YuhKuro/Numlocked/pictures/Front.png

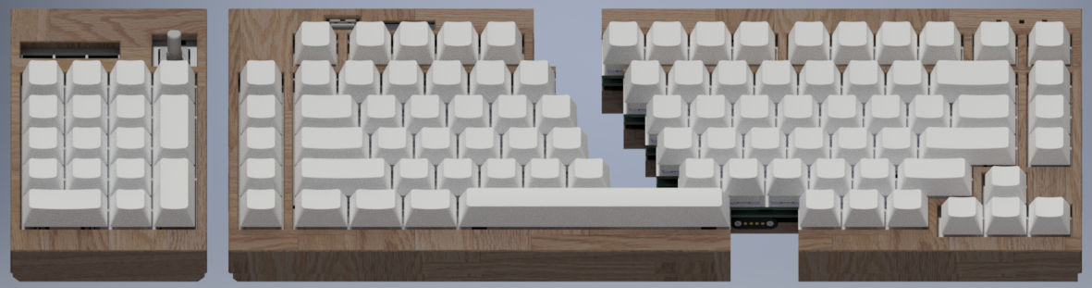
pictures/Front.png
