YuhKuro/Numlocked/pictures/GUIExample.png

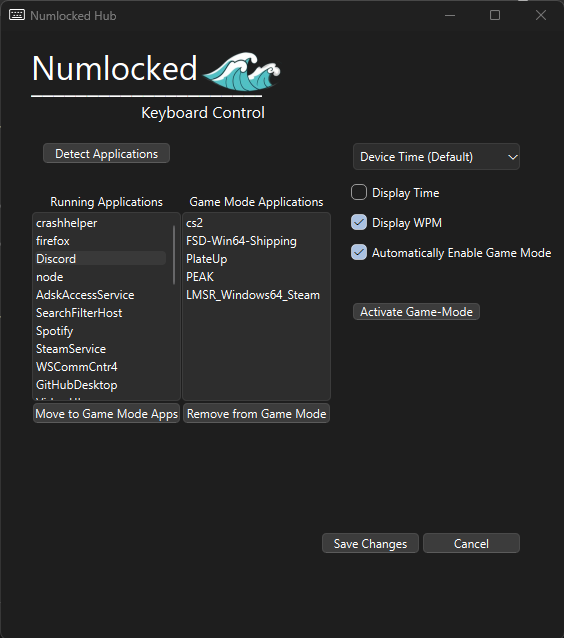
pictures/GUIExample.png
