YuhKuro/Numlocked/pictures/Ortho.png

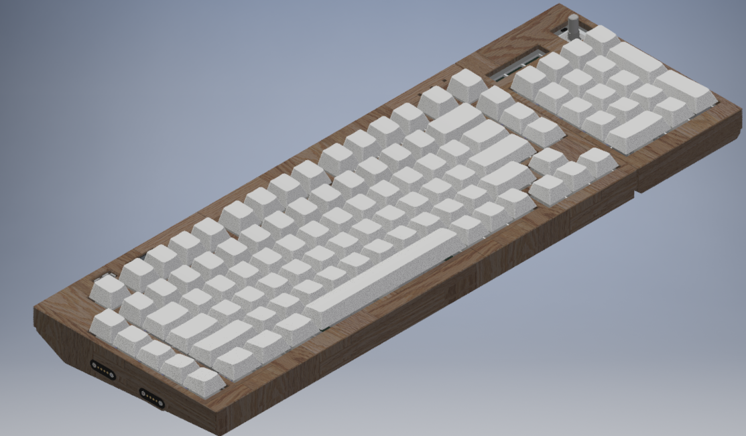
pictures/Ortho.png
