YuhKuro/Numlocked/pictures/PCB Renders/numlocked_shift_PCB3.png

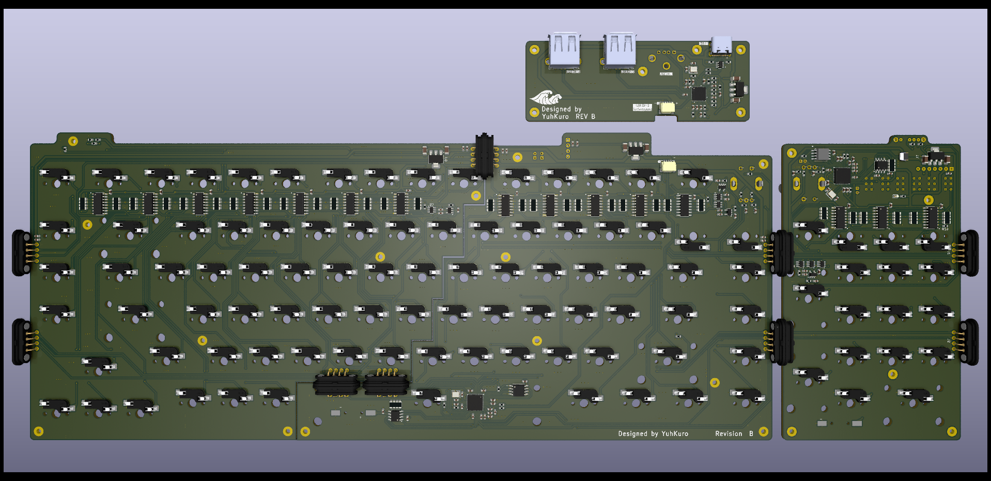
pictures/PCB Renders/numlocked_shift_PCB3.png
