YuhKuro/Numlocked/pictures/PCB Renders/numlocked_shift_PCB.png

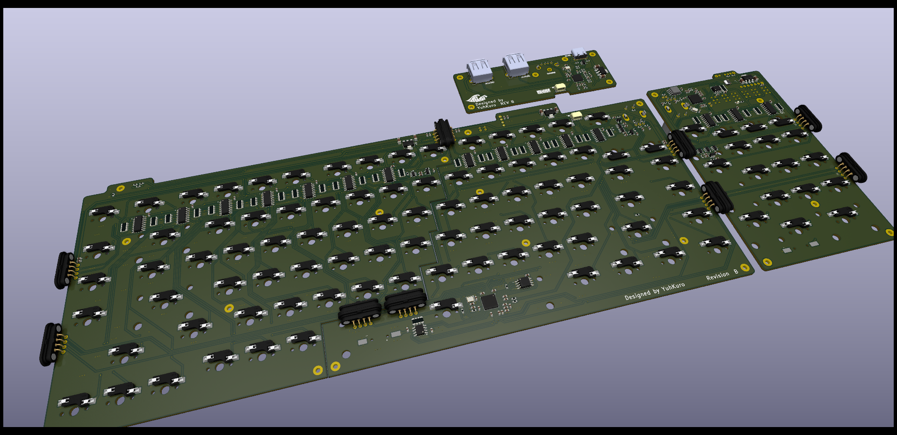
pictures/PCB Renders/numlocked_shift_PCB.png
