YuhKuro/Numlocked/pictures/Rear.png

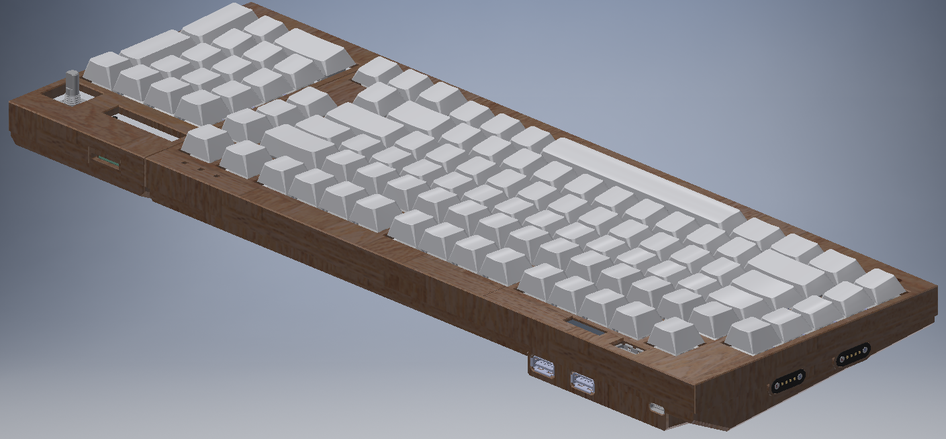
pictures/Rear.png
