YuhKuro/Numlocked/pictures/threeFourthGIF.gif

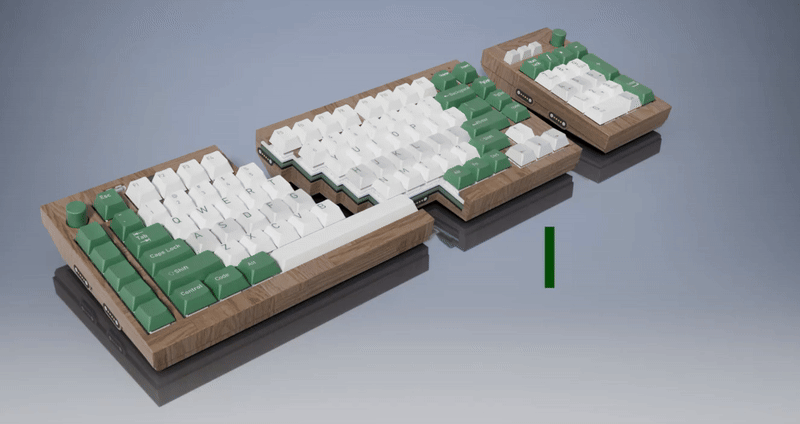
pictures/threeFourthGIF.gif
