YuhKuro/Numlocked/pictures/ThreeFourthGreen.png

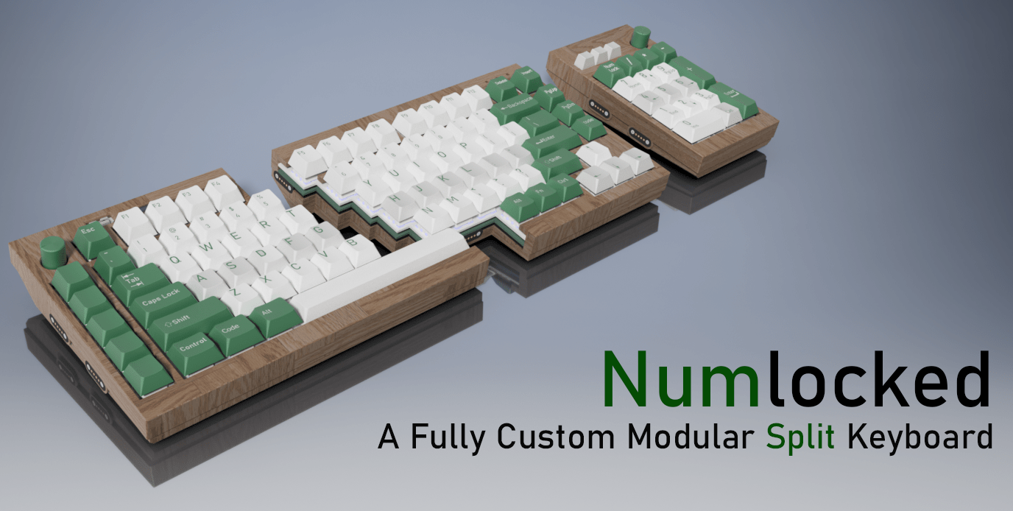
pictures/ThreeFourthGreen.png
