YuhKuro/Numlocked/firmware/bootanim.h

#ifndef _BOOTANIM_H_
#define _BOOTANIM_H_

const unsigned long startUpFrameSize = 642;
const unsigned char startup_frames[10][642] = {{
0x42,0x4d,0x82,0x02,0x00,0x00,0x00,0x00,0x00,0x00,0x82,0x00,0x00,0x00,0x6c,0x00,
0x00,0x00,0x80,0x00,0x00,0x00,0x20,0x00,0x00,0x00,0x01,0x00,0x01,0x00,0x00,0x00,
0x00,0x00,0x00,0x02,0x00,0x00,0x00,0x00,0x00,0x00,0x00,0x00,0x00,0x00,0x02,0x00,
0x00,0x00,0x02,0x00,0x00,0x00,0x00,0x00,0xff,0x00,0x00,0xff,0x00,0x00,0xff,0x00,
0x00,0x00,0x00,0x00,0x00,0xff,0x42,0x47,0x52,0x73,0x00,0x00,0x00,0x00,0x00,0x00,
0x00,0x00,0x00,0x00,0x00,0x40,0x00,0x00,0x00,0x00,0x00,0x00,0x00,0x00,0x00,0x00,
0x00,0x40,0x00,0x00,0x00,0x00,0x00,0x00,0x00,0x00,0x00,0x00,0x00,0x40,0x00,0x00,
0x00,0x00,0x00,0x00,0x00,0x00,0x00,0x00,0x00,0x00,0xff,0xff,0xff,0x00,0x00,0x00,
0x00,0x00,0x3f,0xff,0xff,0xff,0x9f,0xe0,0x0f,0xff,0x80,0xfe,0x7f,0xff,0xff,0xff,
0x9f,0xe0,0xff,0xc0,0x00,0x7f,0xf7,0xf8,0x07,0xfe,0x07,0xf9,0xff,0x80,0x00,0xff,
0xe7,0xf8,0xfc,0x00,0x00,0x0f,0xfd,0xff,0x01,0xf0,0x3f,0xe7,0xfc,0x00,0x00,0x0f,
0xf9,0xff,0xe0,0x80,0x48,0x01,0xff,0x3f,0xfc,0x07,0xff,0x3f,0xe0,0x90,0x40,0x03,
0xfe,0x7f,0xc0,0x10,0x90,0x10,0x7f,0xcf,0xff,0xff,0xfc,0xff,0x82,0x00,0x00,0x00,
0xff,0xdf,0x10,0x09,0x22,0x02,0x1f,0xf3,0xff,0xff,0xe7,0xfe,0x32,0x09,0x00,0x26,
0x3f,0xf3,0x00,0x09,0x00,0x66,0x07,0xfe,0x3f,0xfe,0x3f,0xfc,0x12,0x20,0x00,0x00,
0x0f,0xfe,0xf0,0x00,0x4c,0x26,0x01,0xff,0xe0,0x03,0xff,0xe7,0xf0,0x20,0x1c,0x40,
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
0x00,0x00,0xc1,0xf8,0x3f,0xf0,0x00,0x00,0x00,0x00,0x01,0xff,0xc3,0xf8,0x7f,0xf0,
0x00,0x00,0xff,0xff,0xff,0xc0,0x00,0x00,0x00,0x00,0x00,0x7f,0xff,0xff,0xff,0xc0,
0x00,0x00,0xff,0xff,0xff,0x00,0x00,0x00,0x00,0x00,0x00,0x0f,0xff,0xff,0xfe,0x00,
0x00,0x00,0xff,0xff,0xf8,0x00,0x00,0x00,0x00,0x00,0x00,0x03,0xff,0xff,0xf0,0x00,
0x00,0x00,0x3f,0xff,0x80,0x00,0x00,0x00,0x00,0x00,0x00,0x00,0x3f,0xff,0x80,0x00,
0x00,0x00,0x00,0xe0,0x00,0x00,0x00,0x00,0x00,0x00,0x00,0x00,0x00,0xe0,0x00,0x00,
0x00,0x00,0x3f,0xff,0xc0,0x00,0x00,0x00,0x00,0x00,0x00,0x00,0x7f,0xff,0x80,0x00,
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
}
};

#endif /* _BOOTANIM_H_ */
