YuhKuro/Numlocked/firmware_simple/bootanim.h

#ifndef _BOOTANIM_H_
#define _BOOTANIM_H_

const unsigned long startUpFrameSize = 574;
const unsigned char startup_frames[574] = {'B','M','>',02,0,0,0,0,0,0,'>',0,0,0,'(',0,0,0,0200,0,0,0,' ',0,0,0,01,0,01,0,0,0,0,0,0,02,0,0,0,0,0,0,0,0,0,0,0,0,0,0,0,0,0,0,0,0,0,0,0377,0377,0377,0,0,0,0,0,0,0,0,0,0,07,'p',0,0,0,0,0,0,0,0,0,0,0,0,0,0,06,'`',0,0,0,0,0,0,0,0,0,0,0,0,0,0,07,'p',0,0,0,0,0,0,0,0,0,0,0,0,0,0,07,'p',0,0,0,0,0,0,0,0,0,0,0,0,0,0,07,'p',0,0,0,0,0,0,0,0,0,0,0,0,0,0,07,'x',0,0,0,0,0,0,0,0,0,0,0,0,0,0,07,'p',0,0,0,0,0,0,0,0,0,0,0,0,0,0,03,0370,0,0,0,0,0,0,0,0,0,0,0,0,0,0,01,0360,0,0,0,0,0,0,'?',0340,0,0,0,0,0,0,03,0340,0,0,0,0,0,01,0177,0364,01,'A','P','U',025,05,021,0340,'T','T',024,025,'@',03,0377,0374,03,0343,0370,'?','?',037,0270,0362,0376,'|','>',037,0342,07,'w',0177,07,'w','}','w',0177,'_',0177,0177,0177,'~',037,037,'w',017,0300,017,0207,0377,'?',0343,0371,0375,0377,0377,0377,0377,'>','8','x',037,0,01,0307,'|',07,0301,0361,0370,'w',0374,0307,0307,037,'p','p','>',0,0,0376,'>',07,0,0340,0370,'3',0340,0343,0303,0373,'0',020,'t',0,0,0177,034,07,01,0360,'p','q',0360,'q',0305,0363,'p',020,'x',0,0,'>',036,07,0203,0370,'x','8',0370,0360,0301,0373,0360,0,'p',0,0,037,034,07,0301,0360,'x','|','p','q',0341,0361,0360,0,0360,0,0,016,036,017,0203,0260,'x','8','x','9',0340,0371,0360,0,'p',0,034,037,024,035,'A','<','x',034,'p',037,'@','p','`',0,0340,0,'>',017,0200,015,0343,0270,'0',016,0360,017,0200,' ',0,0,0360,0,'?',05,0,035,0301,034,020,07,0300,05,0,0,0,0,0360,0,'?',0,0,014,0343,0230,0,03,0200,0,0,0,0,0,0360,0,'?',0,0,034,'A',034,034,0,0,0,0,0,0,0,0340,0,'?',0,0,014,0343,0230,'>',0,0,0,0,0,0,0,'p',0,037,0,0,034,'A',034,037,0,0,0,0,0,0,0,'8',0,036,0,0,014,0343,0230,';',0,0,0,0,0,0,0,'|',0,036,0,0,034,'A',034,037,0,0,0,0,0,0,0,'|',0,036,0,0,014,0343,0330,017,0200,0,0,0,0,0,0,036,0,036,0,0,036,'A',0374,07,0300,0,0,0,0,0,0,037,0200,0374,0,0,037,0341,0370,01,0300,0,0,0,0,0,0,};


#endif /* _BOOTANIM_H_ */
